jrucker2004/switch_tester/C3 Equalz/C3 Equalz Tangerine 67g Average.png

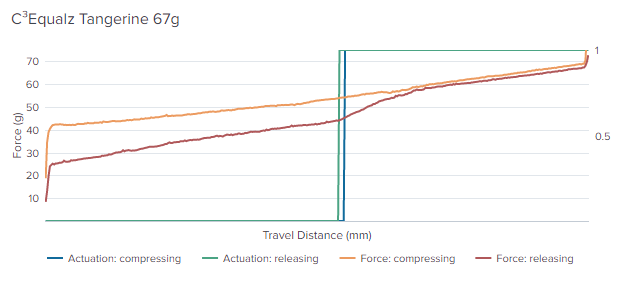
C3 Equalz/C3 Equalz Tangerine 67g Average.png
