jrucker2004/switch_tester/C3 Equalz/C3 Equalz Tangerine 67g Compressing.png

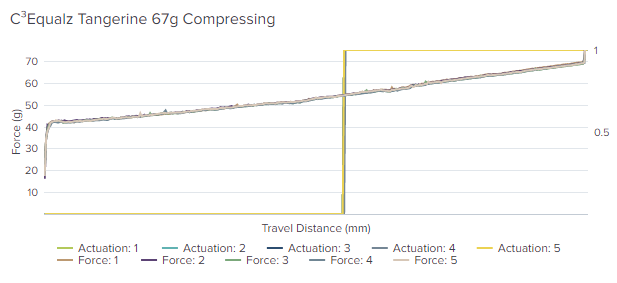
C3 Equalz/C3 Equalz Tangerine 67g Compressing.png
