jrucker2004/switch_tester/Comparisons/Gateron Brown vs Gateron Silent Brown Compressing.png

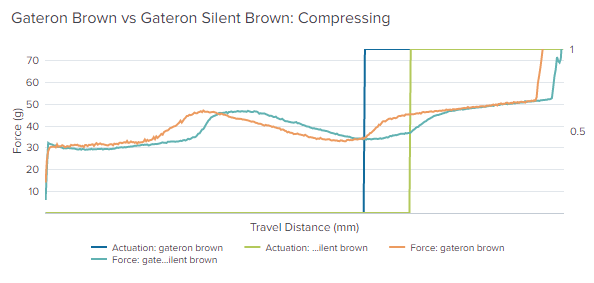
Comparisons/Gateron Brown vs Gateron Silent Brown Compressing.png
