jrucker2004/switch_tester/Comparisons/Gateron Brown vs Gateron Silent Brown Releasing.png

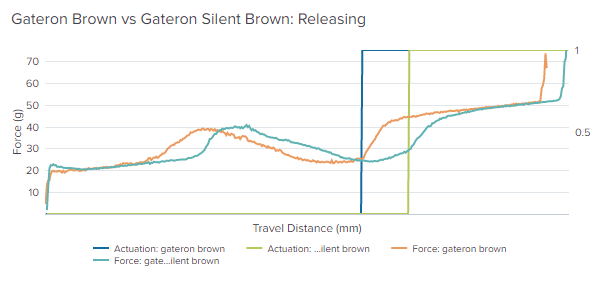
Comparisons/Gateron Brown vs Gateron Silent Brown Releasing.png
