jrucker2004/switch_tester/Durock/Durock T1/Durock T1 67g Average.png

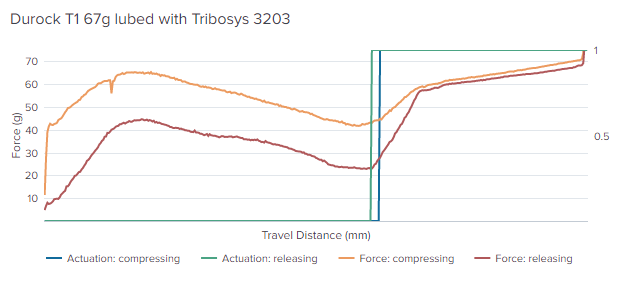
Durock/Durock T1/Durock T1 67g Average.png
