jrucker2004/switch_tester/Frankenswitches/Holy Panda/Holy Panda Average.png

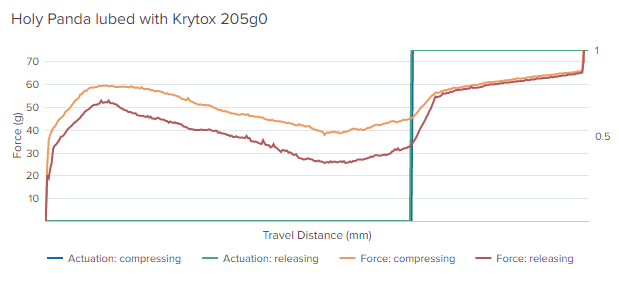
Frankenswitches/Holy Panda/Holy Panda Average.png
