jrucker2004/switch_tester/Frankenswitches/Holy Panda/Holy Panda Compressing.png

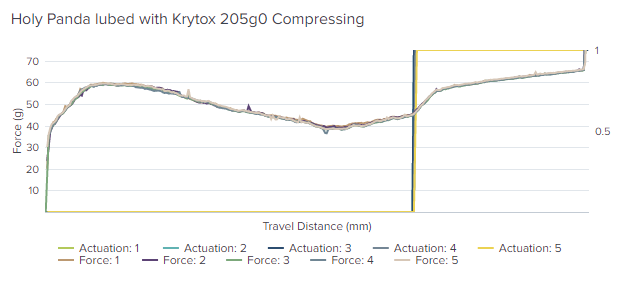
Frankenswitches/Holy Panda/Holy Panda Compressing.png
