jrucker2004/switch_tester/Frankenswitches/Holy Panda/Holy Panda Releasing.png

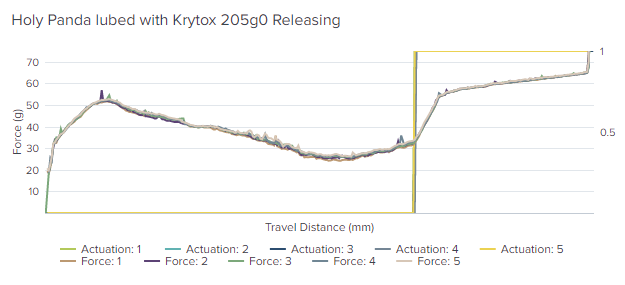
Frankenswitches/Holy Panda/Holy Panda Releasing.png
