jrucker2004/switch_tester/Gateron/Gateron Brown/Gateron Brown Compressing.png

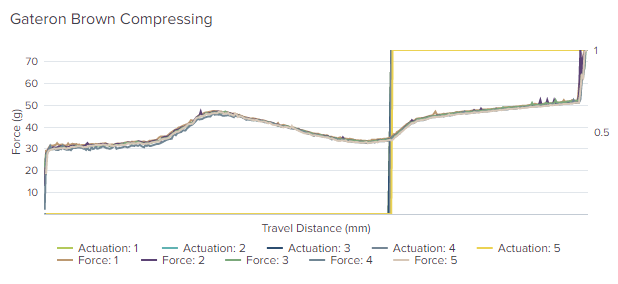
Gateron/Gateron Brown/Gateron Brown Compressing.png
