jrucker2004/switch_tester/Gateron/Gateron Brown/Gateron Brown Releasing.png

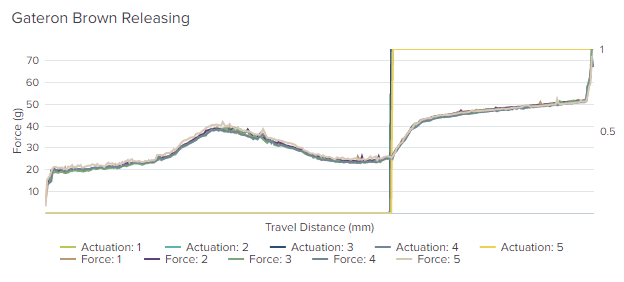
Gateron/Gateron Brown/Gateron Brown Releasing.png
