jrucker2004/switch_tester/Gateron/Gateron Silent Brown/Gateron Silent Brown Average.png

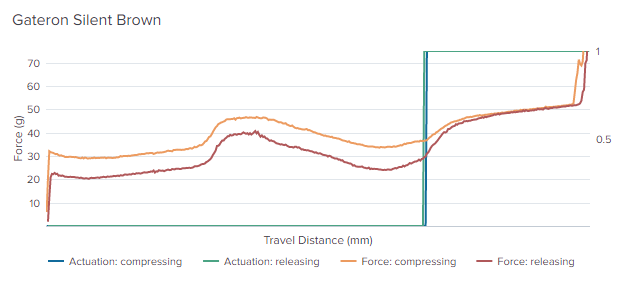
Gateron/Gateron Silent Brown/Gateron Silent Brown Average.png
