jrucker2004/switch_tester/Gateron/Gateron Yellow/Gateron Yellow Average.png

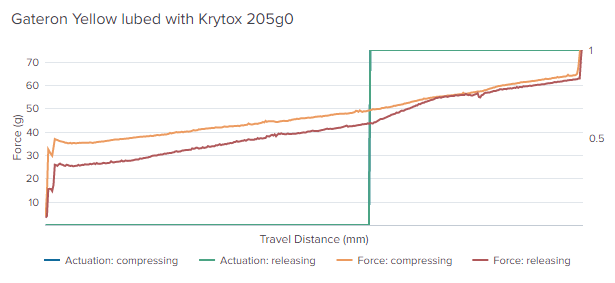
Gateron/Gateron Yellow/Gateron Yellow Average.png
