jrucker2004/switch_tester/Kailh/Kailh Box Navy Average.png

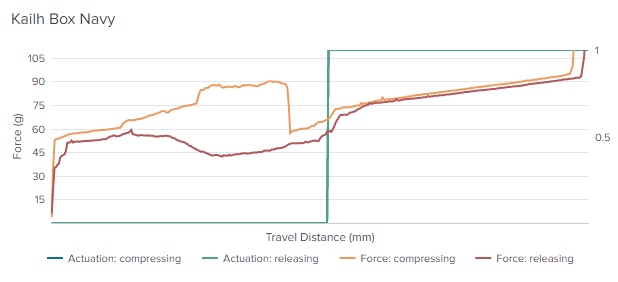
Kailh/Kailh Box Navy Average.png
