jrucker2004/switch_tester/Kailh/Kailh Box Navy Compressing.png

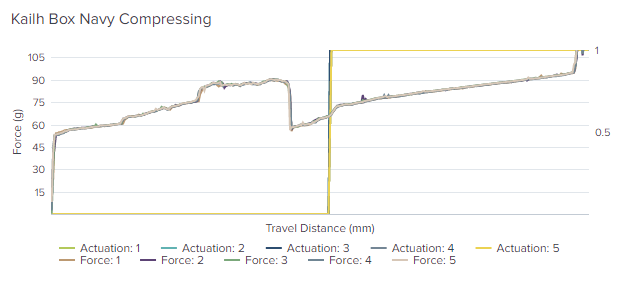
Kailh/Kailh Box Navy Compressing.png
