jrucker2004/switch_tester/Kailh/Kailh Box Navy Releasing.png

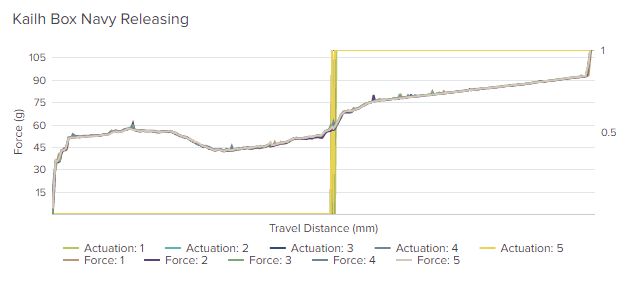
Kailh/Kailh Box Navy Releasing.png
