jrucker2004/switch_tester/Novelkeys/Novelkeys Blueberry/Novelkeys Blueberry Average.png

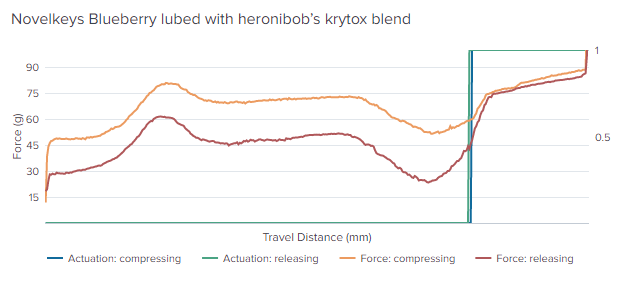
Novelkeys/Novelkeys Blueberry/Novelkeys Blueberry Average.png
