jrucker2004/switch_tester/Novelkeys/Novelkeys Blueberry/Novelkeys Blueberry Compressing.png

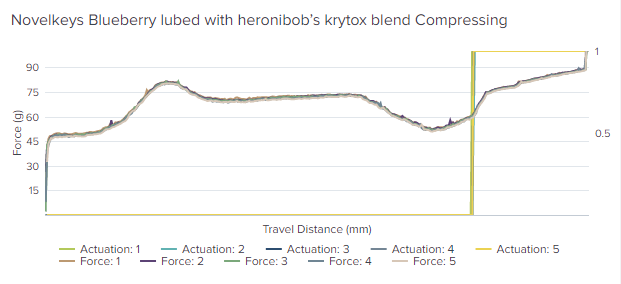
Novelkeys/Novelkeys Blueberry/Novelkeys Blueberry Compressing.png
