jrucker2004/switch_tester/Novelkeys/Novelkeys Blueberry/Novelkeys Blueberry Releasing.png

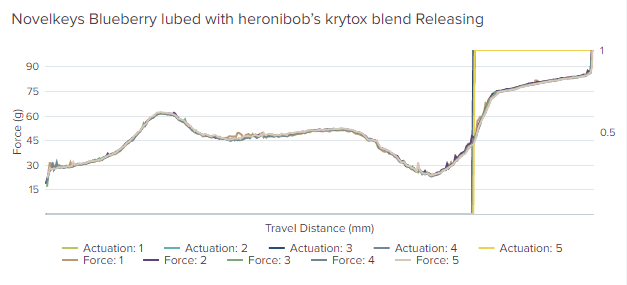
Novelkeys/Novelkeys Blueberry/Novelkeys Blueberry Releasing.png
