jrucker2004/switch_tester/Novelkeys/Novelkeys Cream/Novelkeys Cream Average.png

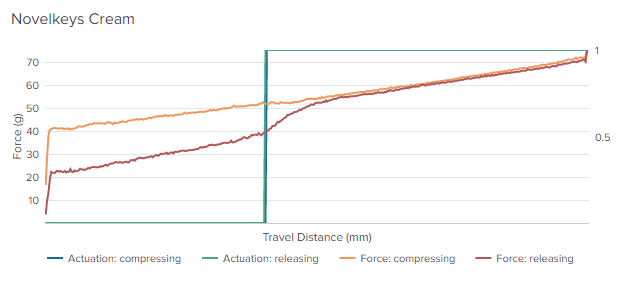
Novelkeys/Novelkeys Cream/Novelkeys Cream Average.png
