jrucker2004/switch_tester/Novelkeys/Novelkeys Cream/Novelkeys Cream Compressing.png

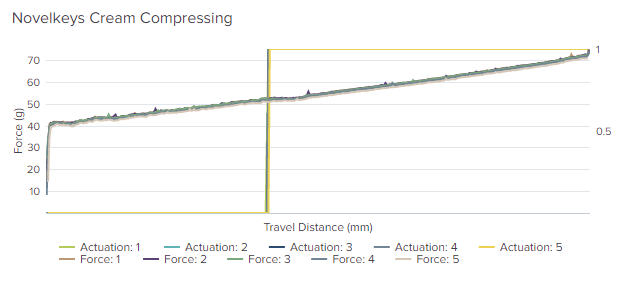
Novelkeys/Novelkeys Cream/Novelkeys Cream Compressing.png
