jrucker2004/switch_tester/Novelkeys/Novelkeys Cream/Novelkeys Cream Releasing.png

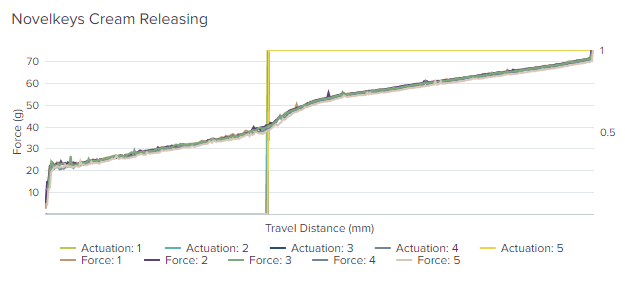
Novelkeys/Novelkeys Cream/Novelkeys Cream Releasing.png
