jrucker2004/switch_tester/Outemu/Outemu Pheonix/Outemu Pheonix 68g Average.png

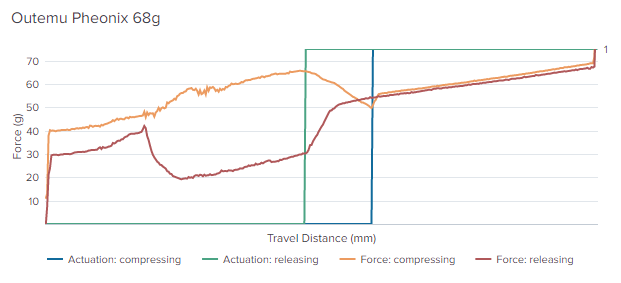
Outemu/Outemu Pheonix/Outemu Pheonix 68g Average.png
