jrucker2004/switch_tester/Outemu/Outemu Pheonix/Outemu Pheonix 68g Releasing.png

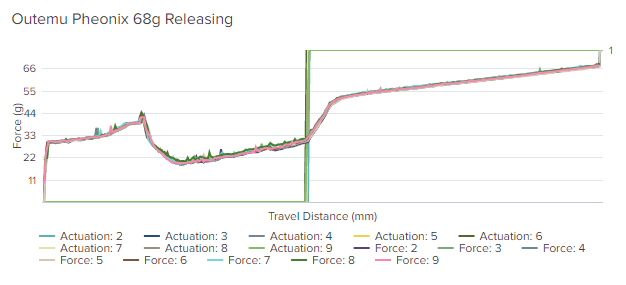
Outemu/Outemu Pheonix/Outemu Pheonix 68g Releasing.png
