jrucker2004/switch_tester/Outemu/Outemu U4 Silent 68g/Outemu U4 Silent 68g Average.png

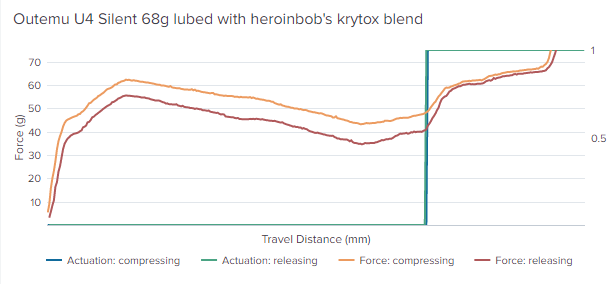
Outemu/Outemu U4 Silent 68g/Outemu U4 Silent 68g Average.png
