jrucker2004/switch_tester/Outemu/Outemu U4 Silent 68g/Outemu U4 Silent 68g Compressing.png

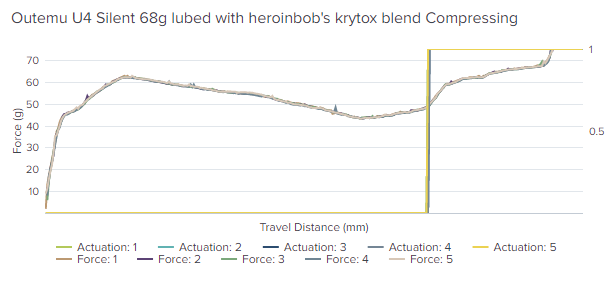
Outemu/Outemu U4 Silent 68g/Outemu U4 Silent 68g Compressing.png
