jrucker2004/switch_tester/Outemu/Sky Silent/Outemu Sky Silent 2.2 68g Compressing.png

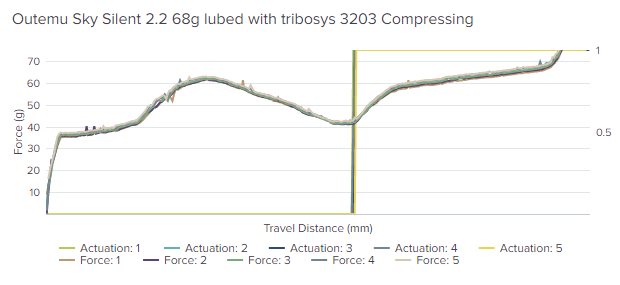
Outemu/Sky Silent/Outemu Sky Silent 2.2 68g Compressing.png
