jrucker2004/switch_tester/Zeal/Zilent V2 65g/Zilent V2 65g Compressing.png

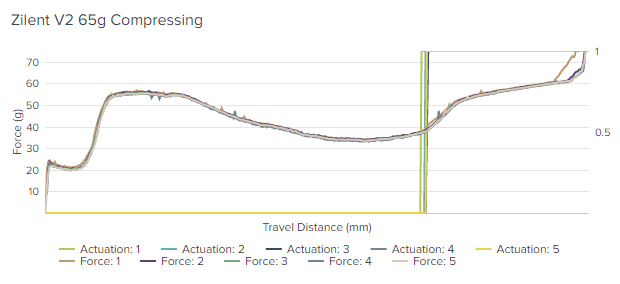
Zeal/Zilent V2 65g/Zilent V2 65g Compressing.png
